daniloc/ThermTerm/src/hardware/WifiInterface.cpp

#include "WifiInterface.h"
#include "_Credentials.h"

WifiInterface::WifiInterface()
{
}

void WifiInterface::configure()
{
    WiFi.begin(WIFI_SSID, WIFI_PASSWORD);

    while (WiFi.status() != WL_CONNECTED)
    {
        delay(1000);
        Serial.println("Connecting to WiFi...");
    }

    Serial.println("Connected to WiFi");
}

WiFiClient &WifiInterface::getWifiClient()
{
    return client_;
}
