daniloc/ThermTerm/src/wifiCredentials.h

#ifndef SRC_WIFICREDENTIALS
#define SRC_WIFICREDENTIALS

char ssid[] = "YOUR_SSID";          // your network SSID (name)
char pass[] = "YOUR_SSID_PASSWORD"; // your network password (use for WPA, or use as key for WEP)

#endif // SRC_WIFICREDENTIALS
